KaetzelLab/Open-MAC/Open-MAC stl design files/9-Com_Bottom_A.stl

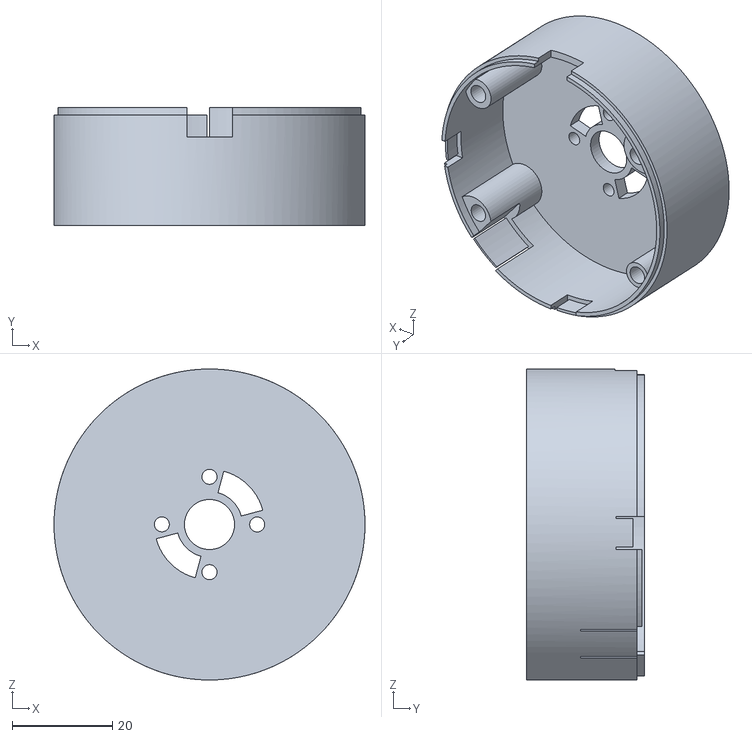
[picture p15: CAD file, 2023-05-17]
Open-MAC stl design files/9-Com_Bottom_A.stl
62.0 x 23.5 x 62.0
